tomsaleeba/ergoslab/misc/chicken.jpg

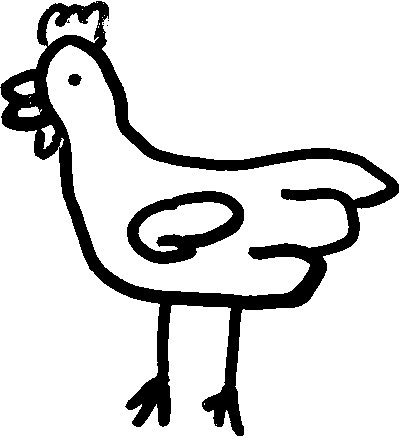
misc/chicken.jpg
