tomsaleeba/ergoslab/misc/swanmatch-moge-naide.jpg

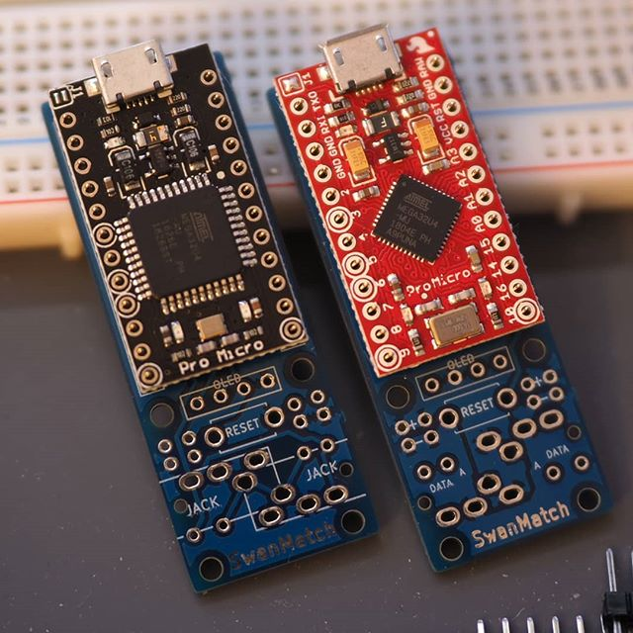
misc/swanmatch-moge-naide.jpg
