tomsaleeba/ergoslab/reference/ws2812.jpg

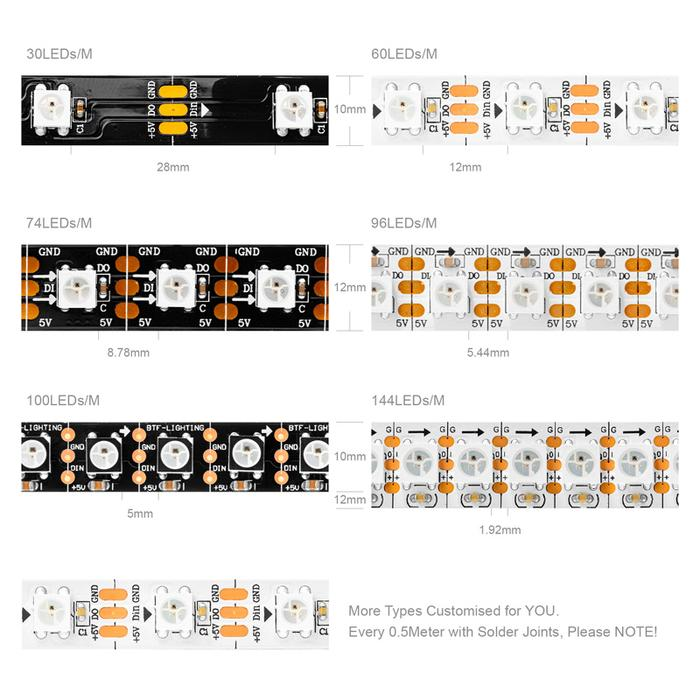
reference/ws2812.jpg
