tomsaleeba/ergoslab/misc/test-layouts/25-2move/layout.png

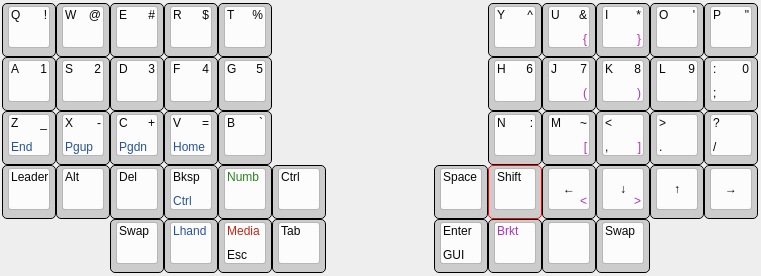
misc/test-layouts/25-2move/layout.png
