tomsaleeba/ergoslab/misc/test-layouts/helix-stagger/layout.png

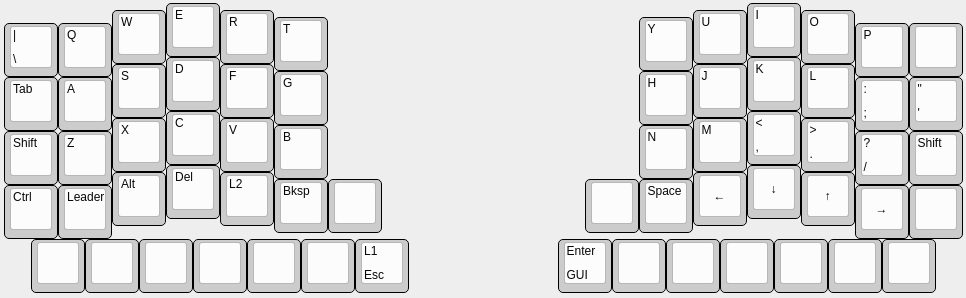
misc/test-layouts/helix-stagger/layout.png
