tomsaleeba/ergoslab/misc/test-layouts/throwing-star-thumb-tester/layout.png

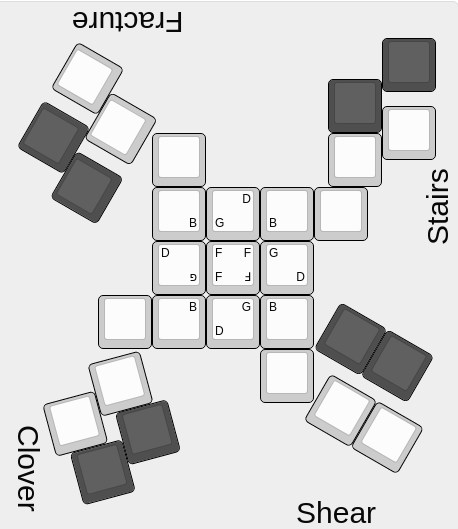
misc/test-layouts/throwing-star-thumb-tester/layout.png
